nurk/8-bit-cpu/application_programmer/input.ino

String serialInput = "";

void readSerial() {
  if (Serial.available() > 0) {
    char incomingByte = Serial.read();

    serialInput += incomingByte;
  }

  if (serialInput.length() > 0 && serialInput.indexOf("\n") == serialInput.length() - 1) {
    if (serialInput.indexOf("test") == 0) {
      Serial.println("Programming test");
      test();
    }
    if (serialInput.indexOf("fibcounter") == 0) {
      Serial.println("Programming fibonacci counter");
      fibonacciInstructionCounter();
    }
    if (serialInput.indexOf("fibonacci") == 0) {
      Serial.println("Programming fibonacci");
      fibonacci();
    }
    if (serialInput.indexOf("countdown") == 0) {
      Serial.println("Programming countdown");
      countDownTest();
    }
    if (serialInput.indexOf("subtract") == 0) {
      Serial.println("Programming subtract");
      subtractTest();
    }
    if (serialInput.indexOf("subroutine") == 0) {
      Serial.println("Programming subroutine");
      subroutenTest();
    }
    serialInput = "";
  }
}
