nurk/8-bit-cpu/InstructionSet/microcode_programmer/input.ino

String serialInput = "";

void readSerial() {
  if (available && Serial.available() > 0) {
    char incomingByte = Serial.read();

    serialInput += incomingByte;
  }

  if (serialInput.length() > 0 && serialInput.indexOf("\n") == serialInput.length() - 1) {
    if (serialInput.indexOf("read") == 0) {
      available = false;
      Serial.println("Reading");
      readEEPROM(8192);
    }
    if (serialInput.indexOf("write") == 0) {
      available = false;
      Serial.println("Writing");
      writeEeprom();
    }
    if (serialInput.indexOf("erase") == 0) {
      available = false;
      Serial.println("Erasing all");
      eraseEEPROM(8192);
    }
    if (serialInput.indexOf("test") == 0) {
      available = false;
      Serial.println("test");
      test();
    }
    serialInput = "";
  }
}
